henriquecgarcia/TCC/_Monografia/Monografia-TCC2 - Henrique Garcia.pdf

Henrique Campanha Garcia

Desenvolvimento de um Veículo Robótico Autônomo de

Pequeno Porte Baseado em ESP32

São José dos Campos, SP

### Henrique Campanha Garcia

## Desenvolvimento de um Veículo Robótico Autônomo de

## Pequeno Porte Baseado em ESP32

Trabalho de conclusão de curso apresentado ao Instituto de Ciência e Tecnologia – UNIFESP, como parte das atividades para obtenção do título de Bacharel em Ciência da Computação.

Universidade Federal de São Paulo – UNIFESP

Instituto de Ciência de Tecnologia

Bacharelado em Ciência da Computação

### Orientador: Prof. Dr. André Marcorin de Oliveira

### São José dos Campos, SP

### Junho de 2026

### Henrique Campanha Garcia

## Desenvolvimento de um Veículo Robótico Autônomo de Pequeno Porte Baseado em ESP32

Trabalho de conclusão de curso apresentado ao Instituto de Ciência e Tecnologia – UNIFESP, como parte das atividades para obtenção do título de Bacharel em Ciência da Computação.

Prof. Dr. André Marcorin de Oliveira Orientador

Prof. Dr. Sérgio Ronaldo Barros dos Santos Convidado 1

Professor
Convidado 2

Professor
Convidado 3

### São José dos Campos, SP Junho de 2026

Dedico este trabalho ao meu orientador, cuja orientação foi essencial para o desenvolvimento deste projeto.

Seus esclarecimentos, especialmente na compreensão e aplicação dos algoritmos envolvidos, foram fundamentais para que eu pudesse superar desafios técnicos e aprofundar meus conhecimentos em áreas que antes me pareciam complexas.

Agradeço pela paciência, disponibilidade e incentivo contínuo ao longo deste processo.

Dedico este trabalho também a todos que, de alguma forma contribuíram para a realização deste projeto.

Muito obrigado.

# Agradecimentos

A realização deste trabalho foi possível graças ao apoio e à colaboração de diversas pessoas e instituições, às quais expresso minha sincera gratidão.

Em primeiro lugar, agradeço ao meu orientador, Prof. Dr. André Marcorin de Oliveira, pelo constante apoio, paciência e pelas valiosas orientações técnicas, especialmente no que diz respeito à compreensão e à implementação dos algoritmos utilizados neste projeto. Sua experiência, dedicação e disponibilidade foram fundamentais para o desenvolvimento desta pesquisa.

Estendo meus agradecimentos à Universidade Federal de São Paulo (UNIFESP), instituição de ensino reconhecida pela excelência acadêmica, pelo compromisso com a formação de profissionais éticos, críticos e preparados para os desafios da sociedade contemporânea.

Aos colegas e amigos que me acompanharam ao longo da graduação, em especial Thiago Capuano e Vinicius Matumoto, sou grato pelos diálogos construtivos, pela colaboração espontânea e, sobretudo, pela amizade que tornou essa caminhada mais leve e motivadora.

À minha família, em especial aos meus pais, Margarete e Renato Garcia, agradeço pelo

amor incondicional, incentivo constante e por acreditarem em mim mesmo diante das dificuldades. Sem o apoio de vocês, este trabalho certamente não teria se concretizado.

Por fim, agradeço a todos aqueles que, direta ou indiretamente, contribuíram para a realização deste projeto.

“Não vos amoldeis às estruturas deste mundo, mas transformai-vos pela renovação da mente, a fim de distinguir qual é a vontade de Deus: o que é bom, o que Lhe é agradável, o que é perfeito. (Bíblia Sagrada, Romanos 12, 2)

# Resumo

Este trabalho apresenta o projeto e desenvolvimento de um veículo robótico autônomo de pequeno porte, concebido para realizar tarefas de transporte de objetos em ambientes internos. O sistema é fundamentado no microcontrolador ESP32, que centraliza o processamento e a conectividade. A percepção do ambiente e a locomoção precisa são viabilizadas pela integração de múltiplos sensores e atuadores, incluindo um magnetômetro QMC5883L para referência de orientação, um sensor de distância Time-of-Flight (ToF) VL53L0X para detecção frontal de obstáculos e encoders ópticos para odometria. O controle de movimento dos motores DC é realizado por meio de uma ponte H com modulação por largura de pulso (PWM), e a estabilidade da trajetória é garantida por um algoritmo de controle Proporcional, Integral e Derivativo (PID). A autonomia de navegação é alcançada por uma estratégia híbrida que combina planejamento de rota global, utilizando o algoritmo A* sobre um mapa de grid, com um controle reativo local para desvio de obstáculos em tempo real. A interação com o usuário é realizada através de uma interface web (WebServer) embarcada, que permite a designação de destinos e o monitoramento do robô via Wi-Fi. O projeto visa entregar um protótipo funcional, de baixo custo e com arquitetura modular, servindo como uma plataforma educacional e de pesquisa em robótica móvel, sistemas embarcados e Internet das Coisas (IoT).

Palavras-chave: Robô Autônomo. ESP32. Controle PID. Navegação Robótica. Mapeamento em Grid. Sistemas Embarcados.

# Abstract

This work presents the design and development of a small-scale autonomous robotic vehicle, designed to perform object transportation tasks in indoor environments. The system is based on the ESP32 microcontroller, which centralizes processing and connectivity. Environmental perception and precise locomotion are enabled by the integration of multiple sensors and actuators, including a QMC5883L magnetometer for heading reference, a VL53L0X Time-of-Flight (ToF) distance sensor for frontal obstacle detection, and optical encoders for odometry. The motion control of the DC motors is performed using an H-bridge with Pulse Width Modulation (PWM), and trajectory stability is ensured by a Proportional, Integral, and Derivative (PID) control algorithm. Navigation autonomy is achieved through a hybrid strategy that combines global path planning, using the A* algorithm on a grid map, with local reactive control for real-time obstacle avoidance. User interaction is carried out through an embedded web interface (WebServer), which allows for destination designation and robot monitoring via Wi-Fi. The project aims to deliver a functional, low-cost prototype with a modular architecture, serving as an educational and research platform in mobile robotics, embedded systems, and the Internet of Things (IoT).

Keywords: Autonomous Robot. ESP32. PID Control. Robotic Navigation. Grid Mapping. Embedded Systems.

# Lista de ilustrações

Figura 6 – Exemplo de mapa 7x7 utilizado para validação do processo de mapeamento. . | 34
Figura 9 – Exemplo de caminho traçado pelo algoritmo A* sobre um mapa de ocupação. | 43
Figura 10 – Interface web do robô mostrando o mapa 7x7, com origem no canto superior

Figura 11 – Interface web principal do robô, exibindo o mapa de ocupação, botões de con-

# Lista de abreviaturas e siglas

ADC | Conversor Analógico-Digital (Analog-to-Digital Converter)
AUV | Veículo Submerso Autônomo (Autonomous Underwater Vehicle)
DC | Corrente Contínua (Direct Current)
GPIO | Pinos de Entrada/Saída de Propósito Geral (General-Purpose Input/Output)
HTTP | Protocolo de Transferência de Hipertexto (Hypertext Transfer Protocol)
IMU | Unidade de Medição Inercial (Inertial Measurement Unit)
IoT | Internet das Coisas (Internet of Things)
IHM | Interface Homem-Máquina
I2C | Inter-Integrated Circuit (padrão de comunicação)
PID | Controlador Proporcional–Integral–Derivativo
PRM | Mapa de Rotas Probabilístico (Probabilistic Roadmap)
PWM | Modulação por Largura de Pulso (Pulse Width Modulation)
RAS | Sistemas Robóticos e Autônomos (Robotic and Autonomous Systems)
RMA | Robôs Móveis Autônomos
RTOS | Sistema Operacional de Tempo Real (Real-Time Operating System)
SLAM | Localização e Mapeamento Simultâneos (Simultaneous Localization and Map- ping)
SPI | Interface Periférica Serial (Serial Peripheral Interface)
ToF | Tempo de Voo (Time-of-Flight)
UART | Transmissor/Receptor Assíncrono Universal (Universal Asynchronous Receiver- Transmitter)
VL53L0X | Sensor ToF da STMicroelectronics
Wi-Fi | Wireless Fidelity (Tecnologia de rede sem fio)
WebServer | Servidor Web embarcado

ESP32 | Microcontrolador com Wi-Fi e Bluetooth integrados da Espressif Systems
QMC5883L | Magnetômetro digital de três eixos utilizado como referência de orientação magnética
A* | Algoritmo A-star para planejamento de caminhos

# Sumário

19

# 1 Introdução

A crescente evolução dos sistemas embarcados e da Internet das Coisas (IoT) tem impulsionado o desenvolvimento de soluções autônomas para aplicações cotidianas. Nesse cenário, veículos autônomos têm despertado interesse pela sua aplicabilidade em tarefas de transporte interno, contribuindo para a automação e otimização de processos, Schilling et al. (1997).

O campo da robótica móvel tem-se desenvolvido significativamente nas últimas décadas, especialmente com a popularização de plataformas modulares e reconfiguráveis Moubarak e Ben-Tzvi (2012) e robôs com capacidade de adaptação a ambientes complexos e dinâmicos Schilling et al. (1997). Nesse contexto, dentro da robótica, os agentes podem ser classificados de acordo com seu grau de autonomia, como por exemplo, robôs teleoperados, semi-autônomos e autônomos. Em todos esses tipos de robôs, e em especial para robôs com graus elevados de autonomia, o uso de sensores embarcados, como unidades de medição inerciais (IMUs) e sensores de distância, em conjunto com algoritmos de controle robustos, como o PID (Proporcional, Integral, Derivativa), têm sido essenciais para garantir precisão e estabilidade Parween et al. (2020).

Dentre as aplicações de sistemas robóticos autônomos, podem ser destacadas os robôs de resgate e salvamento Calisi et al. (2007), Samir et al. (2024), manutenção de submarina Lemos (2021), Nauert e Kampmann (2023), interface com seres humanos em museus Cantucci, Marini e Falcone (2024), Silva e Souza (2024), aplicações militares Studies (2021), Automate.org (2023), entre outros. Em especial, os trabalhos de Nehmzow (2012) e Schilling et al. (1997) destacam a importância de projetos didáticos e aplicáveis de veículos autônomos tanto em ambientes industriais quanto acadêmicos, reforçando a relevância de soluções acessíveis e flexíveis.

Dessa forma, este projeto visa desenvolver um veículo autônomo de pequeno porte com quatro rodas, baseado em um microcontrolador de baixo custo, equipado com magnetômetro, sensor de distância e encoders ópticos. O sistema será capaz de realizar deslocamentos autônomos utilizando mapeamento em grid e planejamento de rotas, com controle remoto por interface web.

A principal motivação do projeto é criar uma solução acessível e didática para transporte interno automatizado em ambientes acadêmicos, facilitando processos de gestão dentro da universidade. Além disso, o desenvolvimento do projeto vai proporcionar o aprendizado multidisciplinar. A contribuição esperada é o desenvolvimento de uma plataforma de baixo custo com potencial de aplicação em ambientes reais, além de servir como base para futuras pesquisas em robótica móvel e IoT.

20 | CAPÍTULO 1. INTRODUÇÃO

## 1.1 Objetivos

Este trabalho tem como finalidade o desenvolvimento de um assistente robótico autônomo voltado à automação de tarefas de transporte de objetos em ambientes internos, como escritórios e residências. A proposta consiste em permitir que o usuário delegue, por meio de uma interface de controle, a entrega de itens a um destino previamente definido, sem a necessidade de deslocamento físico até o local de destino.

Além de propor uma solução prática para aplicações logísticas em pequena escala, o projeto busca consolidar e aplicar os conhecimentos teóricos adquiridos ao longo da graduação, com ênfase nas disciplinas de Sistemas Embarcados, Inteligência Artificial e Internet das Coisas (IoT). A iniciativa visa integrar esses conceitos por meio da construção de um sistema funcional, de baixo custo e alto valor educacional e tecnológico.

### 1.1.1 Objetivo Geral

Desenvolver um protótipo funcional de um veículo robótico autônomo de pequeno porte, dotado de quatro rodas, controlado por um microcontrolador ESP32, e equipado com magnetômetro QMC5883L, sensor de distância por tempo de voo (VL53L0X) e encoders ópticos para monitoramento da rotação das rodas. O sistema deverá ser capaz de se locomover autonomamente em ambientes internos, utilizando mapeamento baseado em grid, planejamento de rotas com A* e definição do destino via interface web.

### 1.1.2 Objetivos Específicos

- Projetar e montar a estrutura física do robô, incluindo os motores, a carcaça e a eletrônica embarcada;
- Implementar controle de velocidade e trajetória utilizando algoritmos PID com feedback dos encoders;
- Integrar o magnetômetro, o sensor de distância e os encoders ópticos ao sistema de controle e navegação;
- Desenvolver o módulo de mapeamento em grid e aplicar algoritmos de busca para planejamento de trajetórias (como o algoritmo A*);
- Implementar uma interface web acessível via rede Wi-Fi, permitindo a seleção de destinos pelo usuário;
- Realizar testes experimentais e validar o desempenho do sistema em ambiente controlado, analisando a precisão, a robustez e a viabilidade da proposta.

1.2. ORGANIZAÇÃO DO TEXTO | 21

## 1.2 Organização do Texto

Este trabalho está estruturado da seguinte forma:

- Capítulo 2 — Revisão Bibliográfica: apresenta uma análise de trabalhos relacionados à robótica móvel autônoma, abordando diferentes aplicações e tecnologias que fundamentam o projeto.
- Capítulo 3 — Fundamentação Teórica: detalha os conceitos teóricos essenciais, incluindo sistemas embarcados, controle de motores, magnetômetro, sensores de distância, odometria por encoders, algoritmos PID, odometria e técnicas de mapeamento e planejamento de rotas.
- Capítulo 4 — Materiais e Métodos: descreve os componentes de hardware e as ferramentas de software utilizadas, a arquitetura do sistema, as estratégias de controle e navegação, e a metodologia de desenvolvimento do protótipo.
- Capítulo 5 — Resultados Parciais: discute os avanços obtidos, a implementação do software de controle, os desafios encontrados e os resultados dos testes individuais com os sensores.
- Capítulo 6 — Conclusão: apresenta as conclusões parciais do trabalho com base nos resultados alcançados e descreve as etapas futuras para a finalização e validação do projeto.

23

# 2 Revisão Bibliográfica

Este capítulo apresenta uma análise de trabalhos relacionados ao desenvolvimento de robôs móveis autônomos, com foco na aplicação em ambientes internos e no transporte de pequenos objetos. São considerados aspectos como autonomia de navegação, controle embarcado, sensoriamento, planejamento de rotas e usabilidade em contextos educacionais ou institucionais. Embora a área de robótica móvel autônoma seja ampla, buscou-se destacar estudos que, direta ou indiretamente, dialogam com os objetivos e desafios deste projeto.

Robôs aplicados a missões de busca e salvamento, como os descritos por Calisi et al. (2007), utilizam estratégias avançadas de exploração e navegação em ambientes não estruturados. Esses robôs são capazes de se orientar em locais desconhecidos e dinâmicos, utilizando sensores embarcados e algoritmos de mapeamento para garantir a segurança da operação. De forma complementar, Samir et al. (2024) apresentam uma revisão sistemática sobre robôs de resgate equipados com inteligência artificial, destacando a integração entre sensoriamento preciso, aprendizado de máquina e planejamento adaptativo em cenários de alto risco. Apesar de operarem em contextos significativamente mais complexos, esses estudos fornecem subsídios importantes sobre navegação segura e sensoriamento embarcado.

Ainda que este projeto se concentre em ambientes internos e controlados, como salas de aula e laboratórios, há paralelos metodológicos com outras aplicações robóticas. Trabalhos como os de Lemos (2021) e Nauert e Kampmann (2023) discutem o uso de veículos submersos autônomos (AUVs) para inspeção de estruturas submarinas, enfrentando desafios técnicos severos, como navegação em seis graus de liberdade e comunicação limitada. Apesar das diferenças no ambiente operacional, ambos os casos compartilham a necessidade de controle embarcado confiável, fusão sensorial e autonomia de locomoção — elementos também centrais para o presente projeto.

Em ambientes públicos e educacionais, Cantucci, Marini e Falcone (2024) investigaram o impacto da autonomia adaptativa de robôs na experiência dos visitantes em museus. Já Silva e Souza (2024) analisam o uso de robôs inteligentes como mediadores culturais em espaços expositivos. Esses estudos destacam a importância da interação com o usuário, da acessibilidade e da robustez na arquitetura de controle. O robô desenvolvido neste projeto, embora mais simples em termos de funcionalidade e escopo, compartilha o objetivo de ser uma ferramenta acessível, intuitiva e funcional em contextos institucionais e educacionais, promovendo uma experiência de uso descomplicada por meio de uma interface web.

Robôs autônomos também são amplamente empregados em aplicações militares e de defesa, conforme discutido em Studies (2021) e Automate.org (2023). Nesses cenários, robustez estrutural, inteligência situacional e operação remota segura são características críticas. Embora o

24 | CAPÍTULO 2. REVISÃO BIBLIOGRÁFICA

projeto aqui apresentado não possua finalidade bélica, ele adota conceitos estruturais semelhantes, como a navegação baseada em sensores, o controle de trajetória via PID e a operação remota via rede sem fio, adaptados para fins acadêmicos e com foco em baixo custo e reprodutibilidade.

No campo da robótica modular, Moubarak e Ben-Tzvi (2012) destacam a importância de plataformas reconfiguráveis, que possibilitam adaptações estruturais para diferentes tipos de missão. Embora o robô desenvolvido neste projeto não possua capacidade de reconfiguração física, adota uma arquitetura modular do ponto de vista do software e da organização dos componentes embarcados. O uso de bibliotecas customizadas, divididas por responsabilidade funcional, favorece a manutenção do sistema e sua expansão futura.

Em síntese, os trabalhos analisados contribuem para o embasamento técnico do projeto, oferecendo diferentes perspectivas sobre sensoriamento, controle e navegação em robôs móveis. O diferencial da proposta apresentada neste TCC reside na sua aplicação prática: a criação de um robô autônomo de pequeno porte, controlado por um ESP32, capaz de realizar o transporte de objetos em ambientes internos por meio de navegação baseada em mapeamento em grid, sensores de distância (VL53L0X), referência magnética de orientação (QMC5883L), algoritmo A* e interface web embarcada. Trata-se de uma solução voltada à didática, ao baixo custo e à possibilidade de replicação em contextos educacionais e institucionais.

25

# 3 Fundamentação Teórica

Este capítulo apresenta os fundamentos teóricos que sustentam o desenvolvimento do projeto, abrangendo os conceitos, tecnologias e métodos necessários para a construção de um veículo robótico autônomo com capacidade de navegação em ambiente interno. A estrutura modular do sistema envolve desde a integração de sensores e atuadores até o controle de movimento e planejamento de rotas.

Inicialmente, são abordados os conceitos de sistemas embarcados e Internet das Coisas (IoT), destacando-se suas arquiteturas e aplicações práticas, bem como a justificativa da escolha do microcontrolador ESP32, amplamente utilizado em projetos que exigem conectividade e capacidade computacional embarcada (Seção 3.1).

Na sequência, são discutidos os princípios de controle de motores de corrente contínua (DC) utilizando circuitos do tipo ponte H, responsáveis por permitir o acionamento bidirecional e o ajuste de velocidade dos motores (Seção 3.2). A Seção 3.5 trata da aplicação do controle PID para estabilização e controle de movimento, bem como do uso de odometria com encoders para estimativa de deslocamento do robô.

Também são explorados os recursos de orientação magnética (Seção 3.3), com destaque para o sensor QMC5883L, que fornece medições do campo magnético nos eixos X, Y e Z para estimativa de direção no plano horizontal. Em seguida, na Seção 3.4, discorre-se sobre sensores de distância baseados no princípio de Time-of-Flight (ToF), como o VL53L0X, cuja precisão e velocidade tornam-no adequado para detecção de obstáculos em tempo real.

Por fim, a Seção 3.6 apresenta as técnicas de representação do ambiente por meio de mapas em grid e os algoritmos de planejamento de rotas, como A* e Dijkstra, que permitem ao robô traçar trajetórias seguras e eficientes até o destino escolhido.

Esses tópicos compõem o corpo teórico necessário para a implementação do sistema proposto, oferecendo suporte conceitual e justificativa técnica para as decisões de projeto. A fundamentação apresentada a seguir baseia-se em referências consolidadas na literatura acadêmica e técnica, como Kurose e Ross (2009), entre outras.

## 3.1 Sistemas Embarcados e IoT

Sistemas embarcados consistem em plataformas computacionais especializadas, compostas por microcontroladores, firmware e, em alguns casos, sistemas operacionais de tempo real (RTOS), cujo propósito é executar tarefas específicas sob restrições rígidas de desempenho, consumo energético e confiabilidade. Essas plataformas integram, de forma sinérgica, componentes de hardware

26 | CAPÍTULO 3. FUNDAMENTAÇÃO TEÓRICA

e software, promovendo soluções otimizadas para diferentes finalidades. Por serem projetados para operar de maneira contínua, eficiente e, frequentemente, em tempo real, os sistemas embarcados desempenham papel central em diversos setores da tecnologia, como automação industrial, controle de processos, equipamentos médicos, monitoramento ambiental e dispositivos de Internet das Coisas (IoT), Carvalho e Neto (2024).

No contexto da IoT, a integração de sistemas embarcados com redes de comunicação sem fio, como Wi-Fi, Bluetooth e LoRa, potencializa a conectividade e a interoperabilidade entre dispositivos distribuídos. Essa conectividade torna possível a criação de ambientes inteligentes, capazes de reagir dinamicamente a estímulos do ambiente, compartilhar dados em tempo real e executar comandos remotos. Entretanto, tais sistemas exigem soluções que conciliem eficiência energética, segurança de dados e escalabilidade, aspectos críticos para aplicações em larga escala, como cidades inteligentes, agricultura de precisão e automação residencial.

Para o desenvolvimento deste projeto, foi selecionado o microcontrolador ESP32, do kit de desenvolvimento DOIT ESP32 Devkit V1, devido à sua ampla versatilidade, baixo custo e rica gama de funcionalidades embarcadas. O ESP32 possui conectividade Wi-Fi e Bluetooth integradas, múltiplos núcleos de processamento, suporte a múltiplos pinos GPIO, conversores analógicodigitais (ADCs), interfaces I2C, SPI e UART, além de timers e recursos de controle PWM, características que o tornam ideal para aplicações embarcadas modernas. A Figura 1 apresenta o diagrama de pinagem da placa, destacando a disposição dos pinos e suas respectivas funcionalidades, informação essencial para a correta conexão dos periféricos utilizados no protótipo.


Figura 1 – Diagrama de pinagem do ESP32.

Fonte: lastminuteengineers.com (https://lastminuteengineers.com/esp32-pinout-reference/)

A escolha do ESP32 justifica-se, portanto, por sua capacidade de processamento superior, ampla conectividade, suporte a múltiplos protocolos de comunicação e integração de periféricos

3.2. CONTROLE DE MOTORES DC E PONTE H | 27

essenciais, reduzindo a necessidade de componentes externos. Além disso, sua popularidade na comunidade de desenvolvimento embarcado proporciona vasta documentação e bibliotecas de código, facilitando o processo de implementação e depuração do sistema.

## 3.2 Controle de Motores DC e Ponte H

Motores de corrente contínua (DC) são componentes amplamente utilizados em plataformas robóticas móveis, especialmente em projetos com sistemas embarcados. Isso se deve à sua construção relativamente simples, ao custo acessível e à capacidade de resposta rápida a comandos de controle. No entanto, para que seja possível controlar de forma eficaz tanto a direção quanto a velocidade desses motores, é necessário empregar circuitos de acionamento apropriados, sendo a ponte H uma das soluções mais utilizadas para esse fim.

A ponte H consiste em um arranjo eletrônico formado geralmente por quatro dispositivos semicondutores de chaveamento (transistores bipolares) dispostos de modo a formar uma topologia semelhante à letra “H”. Esse circuito permite o controle da polaridade da tensão aplicada aos terminais do motor, viabilizando, assim, o acionamento em ambos os sentidos de rotação. Tal característica é fundamental para o deslocamento de robôs autônomos, que requerem comandos precisos de avanço, recuo e curvas, os quais são obtidos por meio do controle individual de cada motor responsável pela movimentação.

Para controlar a velocidade de rotação, é frequentemente empregada a técnica de modulação por largura de pulso (PWM), que ajusta a potência média entregue ao motor pela variação do ciclo de trabalho de um sinal digital. Essa estratégia possibilita uma regulação contínua da velocidade, mantendo a eficiência energética do sistema e reduzindo o desgaste dos componentes eletromecânicos.

A ponte H, portanto, representa uma alternativa consolidada tanto em ambientes educacionais quanto em sistemas de aplicação prática, devido à sua confiabilidade e simplicidade de implementação. Sua interface com microcontroladores, como o ESP32, ocorre por meio de sinais digitais que controlam o estado de cada chave do circuito, permitindo a integração direta com algoritmos de controle embarcados.

A Figura 2 ilustra os dois modos de operação da ponte H, demonstrando como a combinação das chaves eletrônicas determina a direção da corrente elétrica no motor, resultando em rotação no sentido horário ou anti-horário.

## 3.3 Orientação Magnética com QMC5883L

O QMC5883L é um magnetômetro digital de três eixos utilizado para medir componentes do campo magnético nos eixos X, Y e Z. Diferentemente de uma unidade inercial como o MPU6050,

28 | CAPÍTULO 3. FUNDAMENTAÇÃO TEÓRICA


(a) Rotação horária do motor. | (b) Rotação anti-horária do motor.

Figura 2 – Funcionamento da ponte H para diferentes sentidos de rotação.

Fonte: LASTMINUTEENGINEERS, 2024. (https://lastminuteengineers.com/l298n-dc-stepper-driver-arduino-tutorial/)

esse sensor não possui acelerômetro nem giroscópio, de modo que não fornece diretamente aceleração linear, velocidade angular ou temperatura útil para controle de movimento. Sua principal aplicação no contexto deste projeto é fornecer uma referência de orientação absoluta no plano horizontal, calculada a partir da relação entre as componentes magnéticas dos eixos X e Y.

O cálculo do ângulo de orientação, ou heading, é realizado por meio da função atan2, aplicada às leituras convertidas para unidades proporcionais ao campo magnético. Após esse cálculo, podem ser aplicados ajustes de declinação magnética, offsets manuais de calibração e normalização angular para manter o resultado em uma faixa consistente. No protótipo, a classe customizada do QMC5883L mantém uma variável de zero angular, permitindo definir qual leitura deve ser interpretada como referência inicial do robô.

Apesar de sua utilidade como referência global, os testes práticos mostraram que o magnetômetro é sensível a interferências eletromagnéticas provenientes dos motores DC, da ponte H, da bateria e dos cabos de alimentação, além de fontes externas de ruído. Por esse motivo, o QMC5883L não foi adotado como único critério para finalizar curvas. A estratégia mais robusta implementada utiliza os encoders como fonte primária para medir a rotação executada e emprega o magnetômetro apenas como referência auxiliar quando suas leituras estão estáveis.

## 3.4 Sensores Time-of-Flight: VL53L0X

Sensores do tipo Time-of-Flight (ToF), como o modelo VL53L0X, realizam medições de distância com base no tempo que um feixe de luz, geralmente laser infravermelho, leva para atingir um

3.5. ALGORITMOS PID E ODOMETRIA | 29


Figura 3 – Módulo magnetômetro QMC5883L. Fonte: CASA DA ROBOTICA, 2026. (https://www.casadarobotica.com/sensores-modulos/sensores/outros/modulo-bussola-eletronica-magnetometro-hmc5883l)

objeto e retornar ao sensor após a reflexão. Esse princípio de funcionamento permite a obtenção de leituras rápidas e com elevada precisão, alcançando uma resolução na ordem de milímetros e alcance típico de até 1,2 metros em ambientes controlados Industries (2024). Tais características tornam os sensores ToF especialmente adequados para aplicações que requerem resposta em tempo real, como navegação autônoma, detecção e evasão de obstáculos e mapeamento de ambientes tridimensionais.

A escolha do sensor VL53L0X neste projeto se deu, principalmente, por sua superioridade em relação a outros sensores amplamente utilizados no ensino e em projetos de prototipagem, como o HC-SR04. Enquanto o HC-SR04 utiliza ondas ultrassônicas, que estão sujeitas a variações ambientais (como temperatura e tipo de superfície do objeto), o VL53L0X opera com luz, o que lhe confere maior estabilidade, tempo de resposta mais curto e maior precisão nas medições. Dessa forma, o VL53L0X apresenta-se como uma solução mais robusta e confiável para os requisitos do sistema robótico proposto, especialmente no que se refere à detecção eficiente de obstáculos em tempo real e à construção de um mapeamento preciso do ambiente. A representação de um sensor equivalente ao utilizado no projeto está representado na Figura 4.

## 3.5 Algoritmos PID e Odometria

O controle PID é uma das técnicas mais amplamente utilizadas em sistemas de controle automático, especialmente em aplicações embarcadas e robóticas. Sua popularidade advém da simplicidade de implementação e da eficácia no controle de processos dinâmicos. Em robótica móvel, o

30 | CAPÍTULO 3. FUNDAMENTAÇÃO TEÓRICA


Figura 4 – Sensor VL53L0X
Fonte: ARDUINOECIA, 2025. (https://arduinoecia.com.br/product/sensor-de-distancia-vl53l0x-laser-time-of-flight-tof/)

PID é comumente aplicado ao controle de velocidade e posição dos motores, ajustando continuamente os sinais de atuação de acordo com o erro entre o valor desejado (referência) e o valor atual medido.

Matematicamente, a saída de controle u(t) do controlador PID é definida como:

u(t) = Kpe(t) + Ki

∫︁ t

0

e(τ ) dτ + Kd

de(t)
dt | (3.1)

onde:

- e(t) representa o erro entre a referência e a saída do sistema no instante t;
- Kp é o ganho proporcional, que reage à magnitude do erro atual;
- Ki é o ganho integral, que corrige desvios acumulados ao longo do tempo;
- Kd é o ganho derivativo, que antecipa tendências com base na taxa de variação do erro.

A sintonização adequada desses parâmetros (Kp, Ki e Kd) é essencial para garantir estabilidade, tempo de resposta adequado e evitar oscilações ou sobrecargas no sistema, como mostrado em Åström e Hägglund (2006).

Complementarmente ao controle, a navegação precisa em ambientes internos exige a estimativa contínua da posição e da orientação do robô, processo conhecido como odometria. A odometria clássica baseia-se na leitura incremental dos encoders ópticos acoplados às rodas motrizes, que fornecem a quantidade de pulsos gerados conforme as rodas giram. Com base nesses

3.6. MAPEAMENTO EM GRID E PLANEJAMENTO DE ROTAS | 31

dados, é possível calcular o deslocamento linear e angular do robô por integração das variações de posição ao longo do tempo.

Considerando um robô diferencial com duas rodas, os deslocamentos linear ∆s e angular ∆θ são dados por: (SIEGWART; NOURBAKHSH; SCARAMUZZA, 2011)

∆s =

r
2
(∆φR + ∆φL) | (3.2)

∆θ =

r
d
(∆φR − ∆φL) | (3.3)

onde:

- r é o raio das rodas;
- d é a distância entre as rodas;
- ∆φR e ∆φL são os incrementos angulares das rodas direita e esquerda, respectivamente.

Essas equações permitem atualizar a posição do robô em coordenadas cartesianas (x, y)

com base no deslocamento linear e na mudança de orientação, utilizando relações trigonométricas.

Apesar da sua simplicidade, a odometria baseada exclusivamente em encoders está sujeita a erros cumulativos, como deslizamentos de roda e imprecisões de leitura. Para mitigar esses erros, é comum a fusão de sensores, combinando odometria com referências externas de orientação, como o magnetômetro QMC5883L Gonçalves e Silva (2017).

Portanto, a utilização combinada do controle PID e da odometria fornece uma base robusta para a movimentação precisa e a navegação confiável do robô em ambientes internos, atendendo aos requisitos de autonomia e estabilidade do sistema proposto.

## 3.6 Mapeamento em Grid e Planejamento de Rotas

O mapeamento em grid é uma técnica amplamente adotada na área de robótica móvel para representação espacial de ambientes. Essa abordagem consiste na discretização do espaço contínuo em uma matriz bidimensional composta por células uniformes, também conhecidas como grades de ocupação. Cada célula da matriz representa uma região específica do ambiente e pode assumir diferentes estados, como livre, ocupada ou desconhecida, conforme as informações captadas por sensores embarcados durante o deslocamento do robô Oliveira (2020).

Essa representação estruturada facilita a modelagem do ambiente de forma computacionalmente tratável, permitindo a realização de tarefas como planejamento de rotas, evasão de obstáculos e atualização dinâmica do mapa conforme novas medições são realizadas. Além disso,

32 | CAPÍTULO 3. FUNDAMENTAÇÃO TEÓRICA

seu formato matricial é compatível com algoritmos de busca que operam sobre grafos e redes, favorecendo a aplicação de soluções bem estabelecidas em teoria da computação.

Para a geração de trajetórias viáveis dentro desse ambiente discretizado, são utilizados algoritmos clássicos de busca e otimização de caminhos, como Dijkstra, A* (A-star) e métodos baseados em amostragem, como o RRT (Rapidly-Exploring Random Tree). Tais algoritmos visam determinar trajetórias que minimizem um determinado custo (como distância, tempo ou consumo energético), respeitando a topologia do ambiente e a presença de obstáculos. A utilização dessas técnicas é essencial para garantir a autonomia, eficiência e segurança da navegação em ambientes parcialmente ou totalmente desconhecidos.

Neste projeto, o processo de navegação e mapeamento foi desenvolvido em conjunto com o módulo de sensoriamento baseado em sensores Time-of-Flight, conforme descrito na Seção 3.4. Ao invés de gerar o mapa completo em tempo de execução, o robô parte de um mapa já fornecido, sobre o qual executa a navegação e as rotinas de amostragem. Um dos objetivos era o auto-mapeamento, seguindo o modelo de Patel (2021), com as devidas adaptações para utilizar o sensor VL53L0X em substituição ao sensor ultrassônico HC-SR04, com o objetivo de obter maior precisão e menor latência nas medições de distância.

Para a implementação prática, o ambiente foi modelado de forma simplificada, assumindose as seguintes definições geométricas:

- Dimensões do robô: representado por um retângulo de largura W e comprimento L;
- Dimensões do ambiente: representadas por uma área retangular de largura RW e comprimento RL;
- Tamanho da matriz de mapeamento: definido como m × n, onde m =
| RL L
e n =
| RW W
,
correspondendo ao número de células percorríveis no eixo vertical e horizontal, respectivamente.

Essa modelagem permite a construção de uma matriz binária que identifica as áreas acessíveis e intransponíveis, conforme os dados sensoriais obtidos ao longo da movimentação do robô. A Figura 5, extraída da proposta original de Patel (2021), ilustra esse conceito de discretização do espaço.

Com a grade definida, a estratégia de mapeamento baseia-se na movimentação sistemática do robô sobre as células da matriz, percorrendo coordenadas discretas (x, y) e atualizando

o estado de cada célula com base nos dados coletados em tempo real. Na fase experimental, o mapa utilizado foi um grid 7x7 fornecido previamente, que serviu como base para validação da navegação e da amostragem. Para a amostragem final, esse mapa foi expandido para proporções maiores, de forma a representar melhor o ambiente e permitir testes mais próximos de cenários reais.

3.6. MAPEAMENTO EM GRID E PLANEJAMENTO DE ROTAS | 33


Figura 5 – Exemplo simplificado de mapeamento em grid.

A Figura 7 exemplifica um padrão de percurso planejado para cobrir integralmente todas as células da matriz. Tal trajetória garante a coleta de dados em todas as áreas do espaço representado, permitindo a construção do mapa de ocupação fornecido. Contudo, o modelo inspirado em Patel (2021) não permite um grande detalhamento do local caso haja um objeto no meio do caminho, mas dado objeto seja apenas local, como cadeiras, bancos e outras mobílias que não necessariamente ficam em um canto da sala. No entanto, para o escopo deste trabalho, cujo objetivo é validar a navegação autônoma em ambientes estruturados (como corredores e salas com obstáculos predominantemente periféricos), este modelo de mapa de ocupação é considerado suficiente e adequado.

Para a realização da locomoção autônoma do robô dentro do ambiente mapeado, é necessário fornecer uma coordenada de destino, expressa em termos da matriz gerada durante o processo de discretização do espaço. Essa coordenada representa a posição final desejada no grid de ocupação, e deve corresponder a uma célula classificada como livre e acessível, conforme os dados obtidos na etapa de mapeamento.

A execução do deslocamento até essa posição depende do conhecimento da posição atual do robô na matriz. Três hipóteses são consideradas válidas para determinar essa posição com segurança:

- Hipótese 1 — Localização por trajetória anterior: o robô já percorreu previamente parte do ambiente e, portanto, sua posição atual pode ser estimada com base na trajetória registrada, utilizando dados de odometria e sensoriamento contínuo. Essa abordagem assume que não houve perdas significativas de precisão acumulada, como deslizamentos ou ruídos nos sensores (estes sendo reduzidos pelo PID e métodos mencionados na Seção 3.5).

34 | CAPÍTULO 3. FUNDAMENTAÇÃO TEÓRICA


Figura 6 – Exemplo de mapa 7x7 utilizado para validação do processo de mapeamento.

- Hipótese 2 — Ponto de partida fixo: o robô inicia sua operação a partir de uma posição conhecida e previamente definida, geralmente no canto superior esquerdo da matriz, correspondente à coordenada (0, 0). Essa configuração é típica de ambientes controlados, como

laboratórios, nos quais a posição inicial pode ser garantida fisicamente.

- Hipótese 3 — Localização informada manualmente: a posição atual do robô é fornecida manualmente por meio de uma interface externa, seja via sistema de monitoramento, interface gráfica ou inserção direta na interface web embarcada no robô. Essa abordagem é útil em cenários nos quais a posição inicial é identificável visualmente ou quando o sistema é reiniciado em um ponto intermediário do ambiente, contudo, esta hipótese depende do usuário saber identificar com certeza a localização que o robô está.

Com a posição de origem e o destino definidos dentro da matriz, um algoritmo de planejamento de rotas pode ser aplicado, como o A* ou Dijkstra, para determinar o melhor caminho possível entre os dois pontos, levando em consideração os obstáculos registrados e a topologia do ambiente. O caminho gerado é, então, convertido em uma sequência de comandos de movimento

3.6. MAPEAMENTO EM GRID E PLANEJAMENTO DE ROTAS | 35


Figura 7 – Exemplo de trajetória do robô durante o processo de mapeamento.

(direções e distâncias) que são enviados ao sistema de controle do robô para execução em tempo real.

Essa abordagem garante que o robô seja capaz de se deslocar de forma autônoma e eficiente dentro do ambiente previamente mapeado, utilizando a representação discreta do espaço como base para a navegação segura e orientada por rotas. Para lidar com a natureza dinâmica dos ambientes reais, que podem conter obstáculos não mapeados ou móveis (como pessoas), a estratégia de navegação adotada é de natureza híbrida. Ela combina um planejador de caminho global com um controlador reativo local.

- Planejador Global: Utilizando o mapa de grid estático gerado previamente, um algoritmo de busca como o A* ou Dijkstra calcula a rota ótima do ponto de partida ao destino. Essa rota serve como um guia macro para a trajetória do robô.
- Controlador Reativo Local: Durante a execução da trajetória, o sensor VL53L0X monitora continuamente o caminho imediato à frente do robô. Caso um obstáculo inesperado seja detectado, o controlador reativo assume prioridade, pausando ou alterando a trajetória localmente para evitar a colisão, para então tentar retornar ao caminho global planejado.

Essa arquitetura de duas camadas confere ao robô a capacidade de seguir um plano de longo prazo enquanto reage de forma inteligente e segura a eventos imprevistos, aumentando significativamente sua autonomia e robustez.

37

# 4 Materiais e Métodos

Este capítulo descreve, de maneira detalhada, os materiais empregados e os procedimentos metodológicos adotados para o desenvolvimento do protótipo de robô autônomo proposto. A escolha criteriosa dos componentes eletrônicos, sensores e atuadores foi orientada pelas necessidades do sistema, levando em consideração fatores como precisão, custo, disponibilidade e compatibilidade com a plataforma de desenvolvimento utilizada.

São apresentados o ambiente de desenvolvimento de software, as bibliotecas utilizadas, os recursos computacionais embarcados, bem como a lógica de controle implementada no microcontrolador. A metodologia abrange também a integração dos sensores, o controle dos motores, o modelo de mapeamento em grid e a abordagem utilizada para planejamento de rotas.

Do ponto de vista físico, o robô é constituído por uma base de pequeno porte sobre a qual foram fixados os módulos eletrônicos, sensores e motores. O sistema de locomoção é composto por quatro motores DC organizados em pares esquerdo e direito, acionados por meio de um módulo de ponte H baseado no L298N. A orientação auxiliar é obtida por um magnetômetro QMC5883L, enquanto a medição de deslocamento e rotação utiliza encoders ópticos. A detecção de obstáculos frontais é realizada com um sensor de distância do tipo Time-of-Flight, modelo VL53L0X. O controle do sistema e a comunicação com o usuário são realizados via microcontrolador ESP32 com interface web embarcada, acessível por meio de rede Wi-Fi local.

A Figura 8 ilustra a disposição física dos componentes do robô, conforme modelagem realizada em ambiente de prototipação virtual. Essa representação facilita a compreensão do layout físico e da interligação entre os módulos utilizados.

## 4.1 Ambiente de Desenvolvimento

O desenvolvimento do firmware embarcado do robô autônomo foi realizado no Visual Studio Code, utilizando a extensão PlatformIO e o framework Arduino para ESP32. Essa escolha permitiu organizar o projeto em uma estrutura modular, com separação entre código-fonte, bibliotecas customizadas, arquivos de interface web e configurações de compilação.

O uso do PlatformIO facilitou o gerenciamento das dependências, a configuração da placa ESP32, a compilação do projeto e o envio dos arquivos estáticos da interface para a memória flash do microcontrolador. Como a interface web é composta por arquivos HTML, CSS e JavaScript, o suporte a sistemas de arquivos embarcados, como SPIFFS, tornou-se parte importante do fluxo de desenvolvimento.

Além da organização do código, o ambiente também favoreceu a depuração incremental.

38 | CAPÍTULO 4. MATERIAIS E MÉTODOS

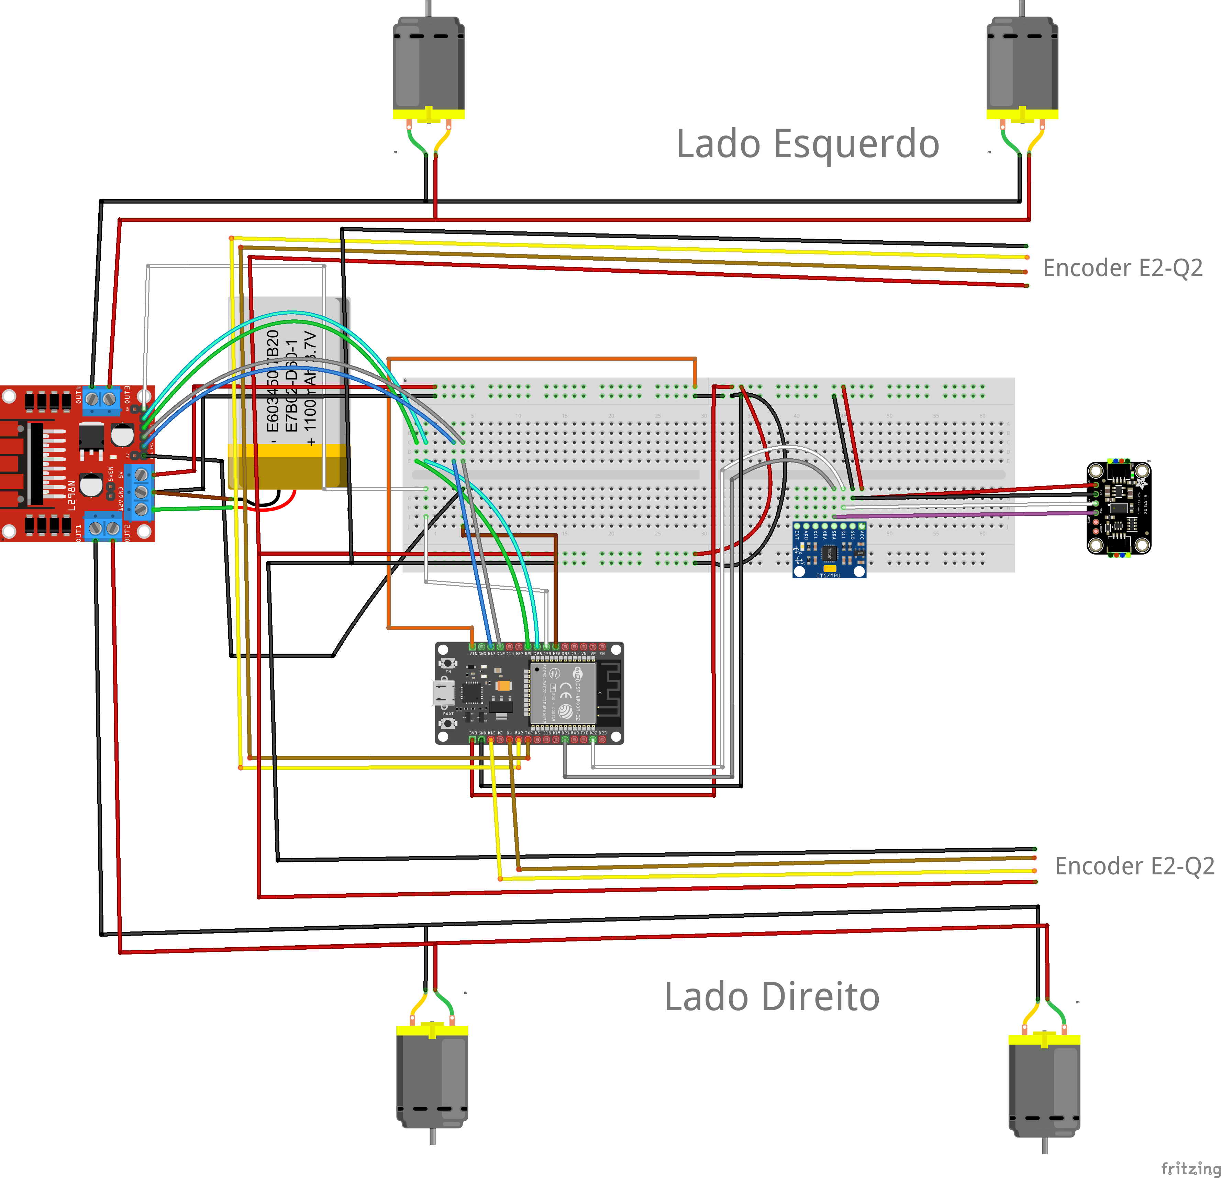
[picture p37: figure]

Figura 8 – Modelo do robô representado em placa de prototipação. Modelo desenvolvido com auxílio da ferramenta Fritzing.org.

Durante o desenvolvimento, logs via serial e via interface web foram utilizados para acompanhar leituras dos encoders, estado do magnetômetro, detecção de obstáculos, planejamento de rota, execução de células e calibração de curvas.

### 4.1.1 Bibliotecas Utilizadas

Para a implementação das funcionalidades do sistema embarcado, foram utilizadas bibliotecas tanto nativas quanto de terceiros. Essas bibliotecas atuaram na abstração de protocolos de comunicação, controle de hardware, gerenciamento de rede e suporte à interface web. A Tabela 1 apresenta as principais bibliotecas utilizadas e suas respectivas finalidades.

### 4.1.2 Bibliotecas Customizadas

A fim de modularizar o sistema, reduzir a complexidade do código-fonte principal e facilitar a manutenção e reuso de funcionalidades, diversas bibliotecas personalizadas foram desenvolvidas especificamente para o projeto. Essas bibliotecas encapsulam funcionalidades críticas como controle de motores, leitura de sensores, filtragem de sinais e gerenciamento de energia. A seguir, são listadas as bibliotecas customizadas implementadas:

4.1. AMBIENTE DE DESENVOLVIMENTO | 39

Tabela 1 – Bibliotecas externas e oficiais utilizadas no projeto

Biblioteca | Finalidade
Wire.h | Comunicação I2C com sensores como QMC5883L e
VL53L0X.
Arduino.h | Funções básicas de controle de pinos, temporização e com-
patibilidade com o ecossistema Arduino.
math.h | Cálculos matemáticos, incluindo trigonometria e manipula-
ção de ponto flutuante.
ArduinoJson.h | Criação e interpretação de objetos JSON para comunicação
com a interface web.
WiFi.h | Conexão do ESP32 à rede Wi-Fi local.
ESPAsyncWebServer.h | Criação de servidor web assíncrono, com suporte a múlti-
plas conexões simultâneas.
SPIFFS.h | Leitura e escrita dos arquivos da interface web no sistema
de arquivos embarcado.
ESPmDNS.h | Resolução de nome de host local usando mDNS, permitindo
acesso por nome amigável.
Adafruit_VL53L0X.h | Controle do sensor de distância VL53L0X.
Adafruit_Sensor.h | Interface comum para sensores Adafruit.
QMC5883L_Custom | Biblioteca própria para configuração, leitura e filtragem do
magnetômetro QMC5883L.
- PID: Implementa o algoritmo de controle Proporcional–Integral–Derivativo, permitindo múltiplas instâncias com parâmetros distintos. Essencial para o controle de velocidade dos motores com base em dados de odometria.
- Filtros e validações: Realizam suavização e validação de leituras, incluindo rejeição de amostras anômalas do QMC5883L e de saltos incompatíveis dos encoders.
- Encoder: Abstrai a leitura dos encoders das rodas, permitindo o cálculo da velocidade, do deslocamento linear e da rotação estimada durante curvas.
- Monitoramento e logs: Agrupa rotinas de diagnóstico utilizadas para registrar telemetria, estado de navegação, erros de sensores e eventos relevantes para calibração.
- VL53L0X (custom): Estende a biblioteca oficial com lógica adicional para detecção de obstáculos com limiares configuráveis.
- QMC5883L (custom): Integra a configuração do magnetômetro, a leitura dos eixos X, Y e Z, o cálculo de heading, a aplicação de offset angular e a rejeição de leituras instáveis.
- Motor: Controla individualmente cada motor, centralizando a lógica de PWM, leitura de encoder e resposta ao PID.
- PonteH: Biblioteca de alto nível responsável pelo controle simultâneo dos motores do robô. Gerencia comandos de movimento, como deslocamento linear, curvas e manobras de rota-

40 | CAPÍTULO 4. MATERIAIS E MÉTODOS

ção no próprio eixo. Também integra informações de sensores para ajuste de trajetória e comunicação em tempo real com a interface web.

A combinação dessas bibliotecas permitiu uma separação clara entre as responsabilidades de cada módulo do sistema, promovendo um desenvolvimento mais organizado, escalável e de fácil manutenção.

## 4.2 Arquitetura do Sistema

A arquitetura do sistema foi projetada com o objetivo de integrar, de maneira modular e eficiente, os diversos componentes eletrônicos e lógicos necessários para o funcionamento autônomo do robô. Essa arquitetura compreende tanto os aspectos físicos (hardware) quanto os elementos de software embarcado, promovendo uma organização funcional que favorece a manutenção, expansão e reutilização de código.

A estrutura física do robô é baseada em uma plataforma de quatro rodas, acionadas por motores de corrente contínua (DC). Cada lado do robô possui dois motores conectados em paralelo, totalizando dois pares (um par esquerdo e outro direito). Os motores frontais de cada par estão equipados com encoders ópticos, responsáveis por fornecer informações sobre a velocidade e o deslocamento linear do robô, fundamentais para a implementação da odometria.

O controle de acionamento dos motores é realizado por meio de um módulo de ponte H baseado no circuito integrado L298N, que permite controlar a direção e a velocidade de cada conjunto de motores de forma independente. Os sinais de controle são enviados pelo microcontrolador ESP32, que atua como unidade central de processamento.

Para sensoriamento, o robô conta com um magnetômetro QMC5883L, utilizado como referência de orientação magnética, e um sensor de distância VL53L0X, posicionado na parte frontal do chassi. O QMC5883L fornece leituras dos eixos X, Y e Z do campo magnético, a partir das quais é calculado o heading do robô no plano horizontal. O VL53L0X é responsável pela detecção de obstáculos à frente, contribuindo para a interrupção segura da navegação e para a avaliação do caminho planejado.

O sistema é alimentado por uma bateria 2S de íon-lítio conectada ao circuito por meio de conector XT60 e chave SS12F46. A alimentação dos motores é encaminhada para o módulo L298N, enquanto o módulo regulador LM2596 fornece 5 V para o ESP32 e sensores. Todos os módulos compartilham referência comum de GND. Toda a lógica de controle, leitura de sensores e comunicação com o usuário é executada no microcontrolador ESP32, utilizando como base a arquitetura modular descrita na Seção 4.1.

A comunicação com o usuário é viabilizada por meio de uma interface web embarcada, acessível via rede Wi-Fi local. Os arquivos HTML, CSS e JavaScript que compõem essa inter-

4.3. ESTRATÉGIAS DE CONTROLE E NAVEGAÇÃO | 41

face estão armazenados na memória flash do microcontrolador, por meio de sistema de arquivos embarcado do SPIFFS. Essa interface permite selecionar destinos, visualizar status de sensores e controlar o robô de forma remota. A troca de dados entre o navegador e o microcontrolador ocorre via WebSockets e objetos JSON, garantindo comunicação bidirecional em tempo real com baixa latência.

## 4.3 Estratégias de Controle e Navegação

A navegação autônoma do robô é composta por um conjunto de estratégias interligadas que envolvem sensoriamento, controle de movimento, estimativa de posição e planejamento de trajetória. O sistema foi projetado para operar de forma reativa e deliberativa, ou seja, combinando a coleta contínua de dados do ambiente com decisões de alto nível baseadas em um mapa interno.

### 4.3.1 Odometria e Estimativa de Posição

A estimativa de deslocamento do robô é realizada por meio da odometria diferencial, utilizando a contagem de pulsos dos encoders ópticos instalados nas rodas frontais. Esses dados são processados para determinar a distância percorrida e a variação angular do robô ao longo do tempo. A equação de atualização da posição baseia-se na integração incremental da velocidade de cada roda, conforme apresentado na Seção 3.5.

A odometria, apesar de eficiente em curtos intervalos de tempo, sofre com acúmulo de erro (deriva) ao longo de percursos maiores. No protótipo atual, os encoders são utilizados como fonte primária para medição de deslocamento e controle de rotação. O magnetômetro QMC5883L é empregado como referência auxiliar de orientação, porém suas leituras são filtradas e rejeitadas quando apresentam saltos incompatíveis com a movimentação esperada, evitando que interferências magnéticas afetem diretamente o controle.

### 4.3.2 Controle de Movimento via PID

O controle de velocidade e direção é implementado por meio de controladores PID, que atuam de forma independente sobre cada lado do robô. Com base nos dados dos encoders, os controladores ajustam dinamicamente a largura de pulso (PWM) aplicada a cada motor, mantendo a velocidade desejada com precisão e compensando variações causadas por carga, atrito ou pequenas diferenças entre os motores.

Durante curvas ou manobras de rotação, a diferença de velocidade entre os lados esquerdo e direito é calculada com base no ângulo alvo definido pelo algoritmo de navegação. A versão atual do sistema utiliza a variação dos encoders como critério principal de parada da rotação, com uma constante de calibração denominada TURN_ENCODER_SCALE. Essa abordagem foi ado-

42 | CAPÍTULO 4. MATERIAIS E MÉTODOS

tada após testes práticos indicarem que o QMC5883L sofre interferências significativas durante o acionamento dos motores.

### 4.3.3 Sensoriamento e Mapeamento do Ambiente

O sensor de distância VL53L0X, posicionado na parte frontal do robô, é utilizado para escanear obstáculos à medida que o robô se desloca. Esses dados são incorporados a uma matriz de ocupação (grid map), que representa o ambiente de forma discretizada. Cada célula da matriz pode assumir o valor de livre, ocupada ou desconhecida, sendo atualizada com base nas medições obtidas em tempo real.

Esse mapeamento em grid fornece ao sistema uma base de conhecimento sobre o ambiente, essencial para o planejamento seguro de trajetórias e para a evasão de colisões com obstáculos fixos ou móveis.

### 4.3.4 Planejamento de Rota com Algoritmo A*

Com base na matriz de ocupação gerada, o planejamento de caminho entre a posição atual e o destino desejado é realizado por meio do algoritmo A* (A-star). Esse algoritmo é amplamente utilizado em sistemas robóticos por combinar eficiência e precisão, realizando uma busca heurística que minimiza o custo total do caminho considerando a distância percorrida e a distância estimada até o objetivo.

O resultado do algoritmo é uma sequência de coordenadas representando a trajetória ideal, a qual é traduzida em comandos de movimento (frente, curva à direita, curva à esquerda, etc.) e enviada ao sistema de controle de baixo nível.

A Figura 9 ilustra um exemplo visual da aplicação do algoritmo A* sobre uma matriz de ocupação, destacando um trajeto seguro entre o ponto de origem e o destino. Embora essa figura não represente o algoritmo efetivamente utilizado pelo robô, ela ajuda a visualizar o princípio de planejamento de caminhos adotado neste trabalho.

Visando a economia de bateria e a eficiência operacional, o sistema de navegação é projetado para seguir a rota planejada de forma otimizada, evitando manobras desnecessárias e reduzindo o tempo total de deslocamento. Nesse sentido, as curvas são penalizadas ao máximo, pois exigem maior esforço ao alterar o sentido de rotação dos motores, consomem mais energia e tendem a tornar a trajetória mais lenta.

### 4.3.5 Execução da Navegação

Após a definição da rota, o robô executa a navegação seguindo as coordenadas obtidas, monitorando continuamente a presença de obstáculos imprevistos por meio do sensor VL53L0X. Caso

4.3. ESTRATÉGIAS DE CONTROLE E NAVEGAÇÃO | 43

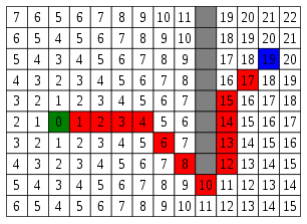
[picture p38: figure]

Figura 9 – Exemplo de caminho traçado pelo algoritmo A* sobre um mapa de ocupação.

Fonte: @nicholas.w.swift at Medium.com (https://medium.com/@nicholas.w.swift/easy-a-star-pathfinding-7e6689c7f7b2)

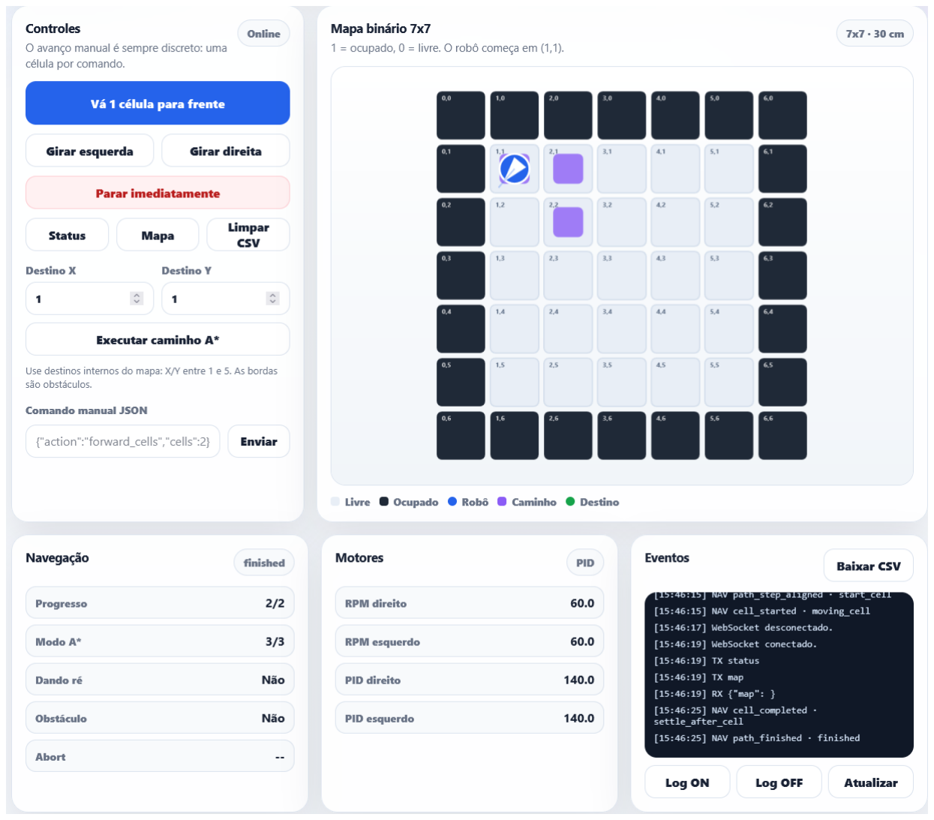
[picture p39: figure]

Figura 10 – Interface web do robô mostrando o mapa 7x7, com origem no canto superior esquerdo, bordas ocupadas e células internas livres.

um obstáculo seja detectado durante o trajeto, o sistema interrompe a locomoção e aborta a execução atual. Na implementação testada, o mapa 7x7 utilizado nos experimentos é preservado, sem sobrescrever células dinamicamente, para evitar que leituras momentâneas do sensor modifiquem a representação base do ambiente durante a calibração. Esse comportamento dinâmico garante maior robustez e segurança na operação em ambientes parcialmente desconhecidos ou com obstáculos móveis.

Essa arquitetura de controle e navegação permite que o robô execute tarefas logísticas simples de forma autônoma, reagindo a estímulos do ambiente e tomando decisões localmente, sem a necessidade de intervenção humana direta.

44 | CAPÍTULO 4. MATERIAIS E MÉTODOS

### 4.3.6 Calibração de Giro e Rejeição de Leituras Instáveis

Durante os testes de rotação, verificou-se que o uso exclusivo do magnetômetro para finalizar curvas não era suficientemente confiável, pois as leituras do QMC5883L apresentavam saltos significativos quando os motores e a ponte H estavam acionados. Para contornar esse problema, a lógica de giro passou a utilizar os encoders como critério principal de parada, com uma constante de calibração denominada TURN_ENCODER_SCALE. Essa constante permite ajustar a relação entre os pulsos medidos pelos encoders e o ângulo físico efetivamente executado pelo robô.

Além disso, foi incorporada uma lógica de rejeição de leituras anômalas. No caso dos encoders, saltos incompatíveis com a velocidade esperada são descartados para evitar que um pulso espúrio encerre uma curva prematuramente. No caso do QMC5883L, leituras com inovação angular excessiva são ignoradas pelo estimador de posição, impedindo que interferências magnéticas atualizem de forma indevida a orientação do robô.

## 4.4 Interface Web e Sistema de Arquivos Flash

A interface web desenvolvida para o sistema permite o monitoramento e controle remoto do robô por meio de um navegador padrão, sem a necessidade de softwares adicionais. Esta interface é hospedada diretamente no microcontrolador ESP32, garantindo autonomia e independência de conexões externas. Os arquivos estáticos, compostos por páginas HTML, folhas de estilo CSS e scripts JavaScript, são armazenados e carregados utilizando o sistema de arquivos LittleFS/SPIFFS, otimizado para dispositivos embarcados com memória limitada.

Para viabilizar a comunicação bidirecional em tempo real entre a interface e o robô, emprega-se o protocolo WebSocket. Esse protocolo possibilita a atualização contínua do status dos sensores, bem como o envio imediato de comandos de movimentação e controle, garantindo uma resposta rápida e eficiente. O uso de WebSocket também minimiza a sobrecarga de comunicação e otimiza o consumo de recursos do ESP32, assegurando estabilidade e desempenho adequados para a aplicação.

## 4.5 Integração e Montagem Mecânica do Robô

O chassi do robô foi projetado e montado utilizando materiais leves e resistentes, priorizando a eficiência energética e a mobilidade. As rodas foram acopladas a motores de corrente contínua equipados com encoders rotativos, permitindo o controle preciso da velocidade e do deslocamento, fundamentais para a implementação de algoritmos de navegação autônoma.

Os sensores foram estrategicamente posicionados para melhorar a confiabilidade das leituras. O sensor ToF foi colocado na região frontal do chassi para detecção de obstáculos no sentido de deslocamento, enquanto o magnetômetro QMC5883L deve permanecer o mais afastado pos-

4.5. INTEGRAÇÃO E MONTAGEM MECÂNICA DO ROBÔ | 45


Figura 11 – Interface web principal do robô, exibindo o mapa de ocupação, botões de controle e telemetria em tempo real.

sível da ponte H, dos motores, da bateria e dos cabos de corrente elevada. A fiação e os cabos foram organizados de forma cuidadosa, utilizando fixadores, para facilitar a manutenção, reduzir interferências eletromagnéticas e evitar danos mecânicos durante o funcionamento.

A alimentação do sistema é fornecida por uma bateria de íon-lítio (Li-ion) 2S, escolhida por sua densidade energética e capacidade de recarga. A distribuição de energia foi organizada com conector XT60, chave SS12F46, regulador LM2596 e módulo L298N. O uso de uma PCB carrier é previsto para reduzir falhas de contato, facilitar a fixação dos módulos e tornar a manutenção elétrica mais segura.

47

# 5 Resultados Parciais

Durante os primeiros meses de desenvolvimento do projeto, foram obtidos avanços significativos na montagem da estrutura física do robô e na integração inicial dos principais componentes eletrônicos e sensores embarcados. A estrutura mecânica foi finalizada de modo a permitir os primeiros testes de campo, os quais revelaram diversas limitações práticas típicas de ambientes reais, como atrito, peso, folgas estruturais, vibrações e desgaste de componentes. Paralelamente, o microcontrolador ESP32 foi programado com um software base, em constante aprimoramento, que possibilita os testes de movimentação e os ajustes dos parâmetros de controle do sistema PID.

## 5.1 Software Utilizado

O desenvolvimento do software embarcado foi realizado utilizando a linguagem de programação da plataforma Arduino, com foco na modularidade e na reusabilidade do código. Foram implementadas diversas classes personalizadas com o intuito de simplificar a interação com os atuadores, sensores e demais rotinas internas do sistema.

Dentre as principais funcionalidades desenvolvidas, destaca-se a criação da classe PID, responsável pela encapsulação do controlador Proporcional–Integral–Derivativo. Esta classe permite a criação de múltiplas instâncias com parâmetros distintos, facilitando o controle individualizado de diferentes motores e situações. Para o tratamento dos dados provenientes do magnetômetro QMC5883L, foi desenvolvida uma classe específica de leitura, filtragem e cálculo de heading, incluindo offsets de calibração e rejeição de amostras com variação angular incompatível com o movimento esperado.

Além disso, foram elaboradas classes específicas para a manipulação do sensor VL53L0X, dos encoders ópticos e do QMC5883L, promovendo maior clareza e organização no código principal. A classe dos encoders, por exemplo, está diretamente associada à classe do motor correspondente, permitindo o cálculo da velocidade e do deslocamento por meio da leitura dos pulsos e da estimativa do RPM. Essas informações são utilizadas para o ajuste dinâmico do sinal PWM, para a medição de distância percorrida e para a estimativa do ângulo executado durante curvas.

As duas classes de motores estão integradas à classe PonteH, que atua como um adaptador de controle dos canais da ponte H. Essa classe centraliza as ações de movimentação, como avanço, ré e rotações, além de gerenciar o acionamento coordenado dos motores de acordo com as decisões do sistema de navegação.

No que tange à interface de comunicação com o usuário, foi desenvolvido um servidor web embarcado que hospeda uma página de visualização em tempo real do estado do robô. Para

48 | CAPÍTULO 5. RESULTADOS PARCIAIS

evitar o excesso de requisições HTTP convencionais, foi implementado um canal de comunicação assíncrona utilizando WebSockets. Essa abordagem permite que o servidor envie atualizações para os clientes sempre que houver alterações relevantes no estado do robô, como mudanças de direção, leituras sensoriais ou atualizações do PID, garantindo maior eficiência e responsividade da interface.

A página web, por ora, apresenta uma interface simplificada com informações em tempo real sobre o sentido do movimento (frente, ré ou rotações), os valores atuais dos sensores embarcados e os parâmetros de controle do sistema.

## 5.2 Problemas Encontrados

Durante os testes iniciais da movimentação autônoma do robô, foi identificada uma falha intermitente no contato elétrico entre a bateria principal e a ponte H, causada pela vibração e deslocamento físico dos conectores durante os deslocamentos. Essa falha ocasionava quedas momentâneas na alimentação dos motores, comprometendo o controle da trajetória e interrompendo as execuções de teste. Após diagnóstico, o problema foi solucionado com a substituição do conector por um modelo mais robusto e seguro, eliminando as interrupções de energia.

Entretanto, novos desafios surgiram com a tentativa de conectar o robô à rede Wi-Fi definida no software. Foram identificadas dificuldades intermitentes na conexão à rede local, o que comprometeu o funcionamento da interface web. Este problema encontra-se em fase de investigação, e possíveis causas incluem instabilidades no sinal, falhas de autenticação ou interferência eletromagnética oriunda de outros componentes do robô.

Em razão dessas instabilidades, especialmente relacionadas ao controle de movimento e conectividade, ainda não foi possível realizar testes completos com os algoritmos de mapeamento e planejamento de rotas. A construção do mapa do ambiente, por depender de uma movimentação precisa e contínua, permanece como uma etapa futura a ser implementada após a estabilização da locomoção e da comunicação do sistema.

## 5.3 Testes com os Sensores

Apesar das dificuldades enfrentadas na integração geral do sistema, os testes individuais dos sensores embarcados mostraram resultados satisfatórios. O sensor de distância VL53L0X apresentou leituras estáveis e responsivas, com tempo de resposta adequado para aplicações de navegação em tempo real. O magnetômetro QMC5883L mostrou-se útil como referência de orientação em repouso ou em condições estáveis, porém apresentou sensibilidade a interferências eletromagnéticas durante o acionamento dos motores. Por esse motivo, sua leitura passou a ser utilizada de forma auxiliar e filtrada, não como critério único para encerramento das curvas.

5.3. TESTES COM OS SENSORES | 49

O controlador de movimento, ainda em fase de ajuste fino, demonstrou capacidade de estabilizar o deslocamento com base no feedback dos encoders, enquanto o controle de rotação passou a depender de calibração específica da odometria angular. Os resultados parciais indicam que a arquitetura proposta é tecnicamente viável e que, com os devidos ajustes e correções, poderá avançar para a fase de integração completa, incluindo mapeamento do ambiente, planejamento de rotas e navegação autônoma.

51

# 6 Validação, Limitações e Próximas Eta-

# pas

Durante os primeiros meses de desenvolvimento do projeto, foram obtidos avanços significativos na montagem da estrutura física do robô e na integração inicial dos principais componentes eletrônicos e sensores embarcados. A estrutura mecânica foi finalizada, permitindo a realização dos primeiros testes de campo, os quais revelaram diversas limitações práticas, como atrito, peso e vibrações. Paralelamente, o microcontrolador ESP32 foi programado com um software base que possibilita os testes de movimentação e os ajustes dos parâmetros de controle do sistema.

## 6.1 Testes e Validação de Componentes

O desenvolvimento do software embarcado foi realizado com foco na modularidade, utilizando a plataforma Arduino. Diversas classes personalizadas foram implementadas para simplificar a interação com os componentes do sistema, das quais se destacam:

- Classes de Controle e Sensores: Foi criada uma classe PID para o controle Proporcional–Integral–Derivativo, uma classe específica para leitura e filtragem do QMC5883L, e abstrações para os encoders ópticos, que calculam a velocidade e o deslocamento.
- Classe de Acionamento: As classes de controle dos motores foram integradas a uma classe PonteH, que centraliza as ações de movimentação, como avanço, ré e rotações.
- Interface Web: Foi desenvolvido um servidor web embarcado com comunicação via Web-Sockets para visualização do estado do robô em tempo real, exibindo informações sobre movimento, sensores e parâmetros do sistema.

Os testes individuais dos sensores embarcados apresentaram resultados satisfatórios. O sensor de distância VL53L0X demonstrou leituras estáveis e responsivas, adequadas para navegação em tempo real. O magnetômetro QMC5883L permitiu a obtenção de uma referência absoluta de orientação, mas os testes evidenciaram que essa referência deve ser usada com filtragem e rejeição de outliers, principalmente devido à interferência causada por motores, bateria, cabos e ponte H. Os encoders mostraram-se essenciais para medir deslocamento e rotação, porém demandaram calibração por meio de uma constante de escala e tratamento contra leituras espúrias. O controlador de movimento, embora ainda em fase de ajuste, demonstrou capacidade de estabilizar o deslocamento com base no feedback dos sensores.

52 | CAPÍTULO 6. VALIDAÇÃO, LIMITAÇÕES E PRÓXIMAS ETAPAS

## 6.2 Desafios e Dificuldades Encontradas

Durante os testes iniciais, foi identificada uma falha intermitente no contato elétrico entre a bateria e a ponte H, causada pela vibração durante os deslocamentos. O problema, que causava quedas de alimentação nos motores e comprometia a trajetória, foi solucionado com a substituição do conector por um modelo mais robusto.

Posteriormente, surgiram novos desafios relacionados à conexão do robô à rede Wi-Fi, com dificuldades intermitentes que comprometeram o funcionamento da interface web. As possíveis causas, como instabilidades no sinal ou interferência eletromagnética, ainda estão em fase de investigação.

## 6.3 Próximas Etapas e Trabalhos Futuros

Em razão das instabilidades de conectividade e da necessidade de refinar o controle de movimento, ainda não foi possível realizar testes completos com os algoritmos de mapeamento e planejamento de rotas. A construção do mapa do ambiente, por depender de uma movimentação precisa, permanece como uma etapa futura a ser implementada após a estabilização completa do sistema.

Os avanços esperados para a finalização do projeto são:

1. Fixação dos cabos e revisão do layout da estrutura física;
2. Estabilização da malha de controle PID para garantir trajetórias previsíveis;
3. Validação do mapeamento em grid 7x7 utilizado nos testes e avaliação de estratégias seguras para atualização dinâmica de obstáculos;
4. Integração do planejamento de rotas com base em A*, usando os dados do mapa definido para o ambiente de teste;
5. Desenvolvimento de interface web responsiva para monitoramento da posição do robô em tempo real;
6. Avaliação do sistema completo em ambiente acadêmico com obstáculos reais e coleta de métricas de desempenho.

Os resultados parciais indicam que a arquitetura proposta é tecnicamente viável e, com os devidos ajustes, poderá avançar para a fase de integração completa e navegação autônoma.

53

# 7 Conclusão Parcial

O desenvolvimento do veículo robótico autônomo baseado em ESP32 demonstrou a viabilidade de uma arquitetura de baixo custo para navegação em ambientes internos. A integração entre motores DC, ponte H L298N, encoders ópticos, sensor ToF VL53L0X, magnetômetro QMC5883L e interface web embarcada permitiu validar os principais blocos necessários para o funcionamento do protótipo.

Os testes realizados indicaram que a navegação por células de aproximadamente 30 cm apresenta resultados promissores, especialmente quando o deslocamento linear é controlado por encoders. Por outro lado, a etapa de rotação exigiu maior refinamento, uma vez que o uso isolado do magnetômetro mostrou-se sensível a interferências eletromagnéticas. Como solução, a versão atual passou a utilizar encoders como referência principal para curvas, com calibração por TURN_ENCODER_SCALE e rejeição de leituras anômalas.

Conclui-se, portanto, que o protótipo possui uma base funcional adequada para continuidade do projeto, mas ainda depende de ajustes finos no controle de giro, fixação elétrica e validação experimental em ambiente controlado. As próximas etapas devem priorizar a consolidação da PCB, a coleta sistemática de métricas de navegação, a inserção de imagens e diagramas finais e a comparação entre o desempenho planejado e o comportamento observado nos testes.

55

# Referências

AUTOMATE.ORG. Service Robots: Defense. 2023. Disponível em: <https://www.automate.org/robotics/service-robots/service-robots-defense>. (https://www.automate.org/robotics/service-robots/service-robots-defense)

CALISI, D. et al. Autonomous exploration for search and rescue robots. In: Safety and Security Engineering II. [S.l.]: WIT Press, 2007. p. 305–314.

CANTUCCI, F.; MARINI, M.; FALCONE, R. Effects of robot’s adaptive autonomy on users experience in a museum scenario. In: CEUR Workshop Proceedings. [s.n.], 2024. v. 3735, p. 1–10. Disponível em: <https://ceur-ws.org/Vol-3735/paper_01.pdf>.

CARVALHO, F.; NETO, A. F. Sistemas embarcados: Fundamentos, aplicações e desafios tecnológicos. Revista Matiz Online, v. 14, p. 1–20, 2024. Instituto Matonense Municipal de Ensino Superior. Disponível em: <https://immes.edu.br/wp-content/uploads/2025/05/Artigo_MATIZ_2024_Sistemas_Embarcados.pdf>. (https://immes.edu.br/wp-content/uploads/2025/05/Artigo_MATIZ_2024_Sistemas_Embarcados.pdf)

GONçALVES, J.; SILVA, M. Odometria visual para robôs. [S.l.], 2017. Disponível em: <https://www.ic.unicamp.br/~reltech/PFG/2017/PFG-17-19.pdf>.

INDUSTRIES, A. Adafruit VL53L0X Time of Flight Micro-LIDAR Distance Sensor Breakout. [S.l.], 2024. Disponível em: <https://cdn-learn.adafruit.com/downloads/pdf/adafruit-vl53l0x-micro-lidar-distance-sensor-breakout.pdf>. (https://cdn-learn.adafruit.com/downloads/pdf/adafruit-vl53l0x-micro-lidar-distance-sensor-breakout.pdf)

KUROSE, J. F.; ROSS, K. W. Computer Networking: A Top-Down Approach. 5. ed. USA: Addison-Wesley, 2009.

LEMOS, J. V. A. Veículos Submersos Autônomos (AUV’s): inspeção e manutenção de estruturas submarinas. Tese (Doutorado) — Universidade Federal de Pernambuco, 2021. Disponível em: <https://repositorio.ufpe.br/bitstream/123456789/48987/1/JO%C3%83O%20VICTOR%20ALMEIDA%20LEMOS.pdf>. (https://repositorio.ufpe.br/bitstream/123456789/48987/1/JO%C3%83O%20VICTOR%20ALMEIDA%20LEMOS.pdf)

MOUBARAK, P.; BEN-TZVI, P. Modular and reconfigurable mobile robotics. Robotics and Autonomous Systems, v. 60, n. 12, p. 1648–1663, 2012. ISSN 0921-8890. Disponível em: <https://www.sciencedirect.com/science/article/pii/S0921889012001480>.

NAUERT, S.; KAMPMANN, P. Inspection and maintenance of industrial infrastructure: challenges and perspectives for autonomous underwater intervention. Frontiers in Robotics and AI, v. 10, p. 1240276, 2023.

NEHMZOW, U. Mobile robotics: a practical introduction. [S.l.]: Springer Science & Business Media, 2012.

OLIVEIRA, A. O uso do algoritmo Mapa de Rotas Probabilístico na robótica móvel. Dissertação (Mestrado) — Universidade Federal de Lavras, 2020. Disponível em: <http://repositorio.ufla.br/bitstream/1/45521/1/MONOGRAFIA_O%20uso%20do%20algoritmo%20Mapa%20de%20Rotas%20Probabil%C3%ADstico%20na%20rob%C3%B3tica%20m%C3%B3vel.pdf>. (http://repositorio.ufla.br/bitstream/1/45521/1/MONOGRAFIA_O%20uso%20do%20algoritmo%20Mapa%20de%20Rotas%20Probabil%C3%ADstico%20na%20rob%C3%B3tica%20m%C3%B3vel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)

PARWEEN, R. et al. Autonomous self-reconfigurable floor cleaning robot. IEEE Access, v. 8, p. 114433–114442, 2020. ISSN 2169-3536.

56 | Referências

PATEL, V. B. Ultrasonic-SLAM. 2021. <https://github.com/PatelVatsalB21/Ultrasonic-SLAM>. Acesso em: 27 jun. 2025.

SAMIR, A. et al. A review of features and characteristics of rescue robot with ai. International Journal of Robotics, v. 12, n. 4, p. 123–145, 2024.

SCHILLING, K. et al. Design of flexible autonomous transport robots for industrial production. In: Proceedings of the IEEE International Symposium on Industrial Electronics (ISIE ’97). [S.l.: s.n.], 1997. p. 791–796.

SIEGWART, R.; NOURBAKHSH, I. R.; SCARAMUZZA, D. Introduction to Autonomous Mobile Robots. 2. ed. Cambridge, MA: MIT press, 2011.

SILVA, L.; SOUZA, A. Robotics and ai in museums – the future of the present. Extrica, v. 12,
n. 4, p. 45–56, 2024. Disponível em: <https://www.extrica.com/article/24355>.

STUDIES, T. H. C. for S. The Military Applicability of Robotic and Autonomous Systems. [S.l.], 2021. Disponível em: <https://hcss.nl/wp-content/uploads/2021/01/RAS_Military_Applicability_Final_.pdf>. (https://hcss.nl/wp-content/uploads/2021/01/RAS_Military_Applicability_Final_.pdf)

ÅSTRöM, K. J.; HäGGLUND, T. Advanced PID Control. Research Triangle Park, NC: ISA—The Instrumentation, Systems, and Automation Society, 2006.
